AJain9199/AOS16/AOS16 Register/AOS16 Register.kicad_pcb

## KiCad design AOS16 Register/AOS16 Register.kicad_pcb (2025-02-15)

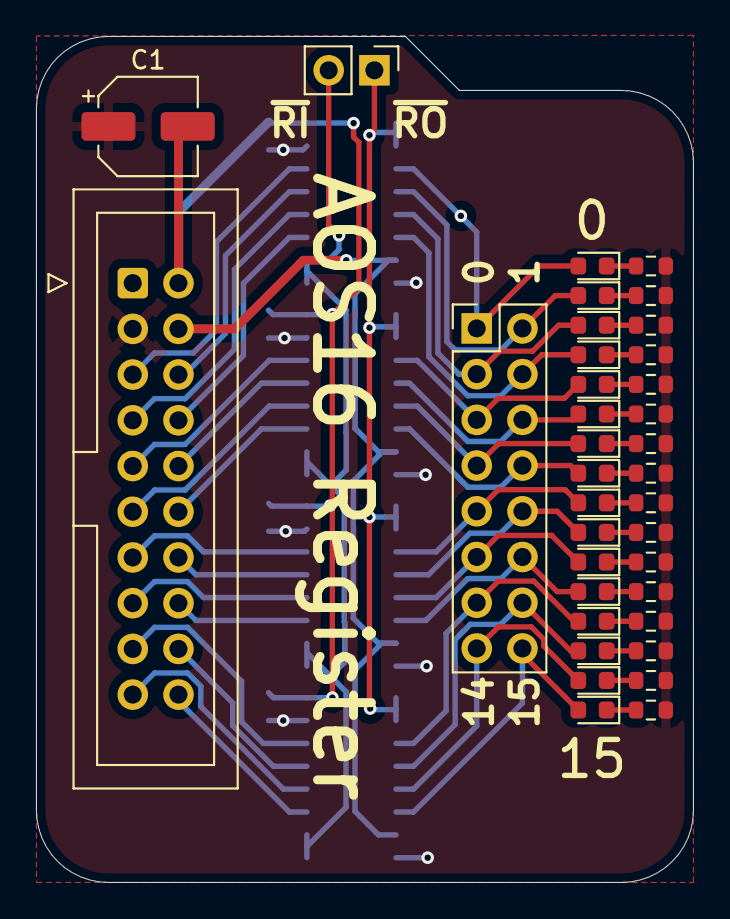
[picture p50: board AOS16 Register.kicad_pcb from above]

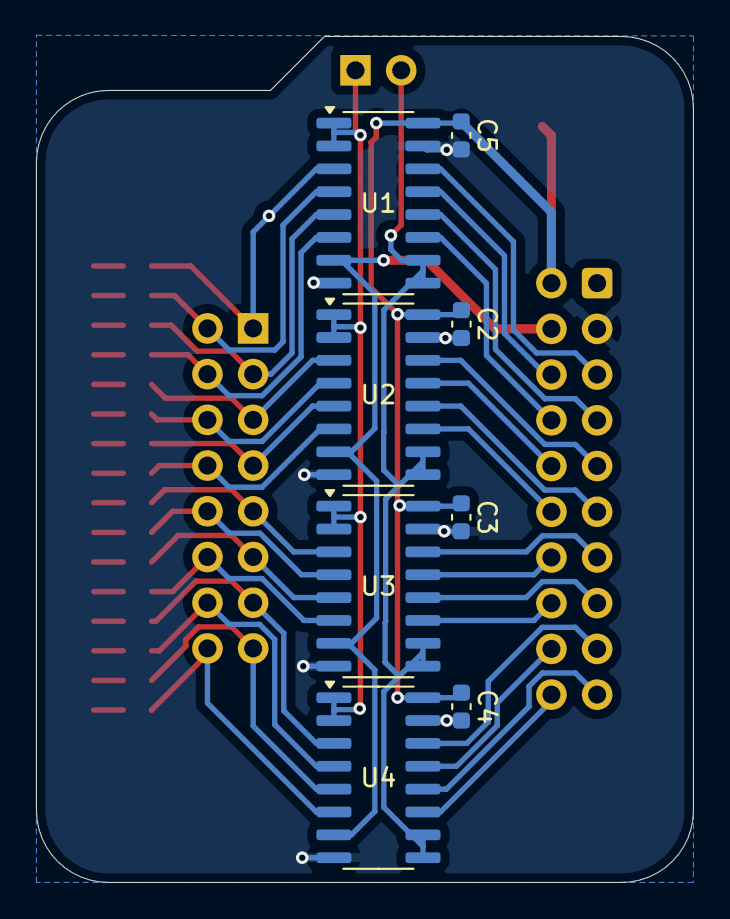
[picture p51: board AOS16 Register.kicad_pcb from below]

Board: 2 copper layers, 36.5 x 47.0 mm, 44 parts (8 on the bottom side), 53 nets.

Parts:
C1: 100uF; CP_Elec_5x5.3
C2, C3, C4, C5: 0.1uF; C_0603_1608Metric
D1, D2, D3, D4, D5, D6, D7, D8, D9, D10, D11, D12, D13, D14, D15, D16: LED; LED_0603_1608Metric
J1: Conn_01x02_Pin; PinHeader_1x02_P2.54mm_Vertical
J2: Conn_02x10_Odd_Even; IDC-Header_2x10_P2.54mm_Vertical
J3: Conn_02x08_Top_Bottom; PinHeader_2x08_P2.54mm_Vertical
R1, R2, R3, R4, R5, R6, R7, R8, R9, R10, R11, R12, R13, R14, R15, R16: R_Small; R_0603_1608Metric
U1, U2, U3, U4: 74HC173; SOIC-16_3.9x9.9mm_P1.27mm

Connections:
/CLK: J2.4, U1.7 (Cp), U2.7 (Cp), U3.7 (Cp), U4.7 (Cp)
/DOUT0: D1.2 (A), J3.1, U1.3 (Q0)
/DOUT1: D2.2 (A), J3.2, U1.4 (Q1)
/DOUT2: D3.2 (A), J3.3, U1.5 (Q2)
/DOUT3: D4.2 (A), J3.4, U1.6 (Q3)
/DOUT4: D5.2 (A), J3.5, U2.3 (Q0)
/DOUT5: D6.2 (A), J3.6, U2.4 (Q1)
/DOUT6: D7.2 (A), J3.7, U2.5 (Q2)
/DOUT7: D8.2 (A), J3.8, U2.6 (Q3)
/DOUT8: D9.2 (A), J3.9, U3.3 (Q0)
/DOUT9: D10.2 (A), J3.10, U3.4 (Q1)
/DOUT10: D11.2 (A), J3.11, U3.5 (Q2)
/DOUT11: D12.2 (A), J3.12, U3.6 (Q3)
/DOUT12: D13.2 (A), J3.13, U4.3 (Q0)
/DOUT13: D14.2 (A), J3.14, U4.4 (Q1)
/DOUT14: D15.2 (A), J3.15, U4.5 (Q2)
/DOUT15: D16.2 (A), J3.16, U4.6 (Q3)
/IO0: J2.5, U1.14 (D0)
/IO1: J2.6, U1.13 (D1)
/IO2: J2.7, U1.12 (D2)
/IO3: J2.8, U1.11 (D3)
/IO4: J2.9, U2.14 (D0)
/IO5: J2.10, U2.13 (D1)
/IO6: J2.11, U2.12 (D2)
/IO7: J2.12, U2.11 (D3)
/IO8: J2.13, U3.14 (D0)
/IO9: J2.14, U3.13 (D1)
/IO10: J2.15, U3.12 (D2)
/IO11: J2.16, U3.11 (D3)
/IO12: J2.17, U4.14 (D0)
/IO13: J2.18, U4.13 (D1)
/IO14: J2.19, U4.12 (D2)
/IO15: J2.20, U4.11 (D3)
/~IE: J1.2, U1.9 (E1), U1.10 (E2), U2.9 (E1), U2.10 (E2), U3.9 (E1), U3.10 (E2), U4.9 (E1), U4.10 (E2)
/~OE: J1.1, U1.1 (Oe1), U1.2 (Oe2), U2.1 (Oe1), U2.2 (Oe2), U3.1 (Oe1), U3.2 (Oe2), U4.1 (Oe1), U4.2 (Oe2)
GND: C1.1, C2.2, C3.2, C4.2, C5.2, J2.3, R1.2, R2.2, R3.2, R4.2, R5.2, R6.2, R7.2, R8.2, R9.2, R10.2, R11.2, R12.2, R13.2, R14.2, R15.2, R16.2, U1.8 (GND), U1.15 (Mr), U2.8 (GND), U2.15 (Mr), U3.8 (GND), U3.15 (Mr), U4.8 (GND), U4.15 (Mr)
unnamed: D1.1 (K), R1.1
unnamed: D2.1 (K), R2.1
unnamed: D3.1 (K), R3.1
unnamed: D4.1 (K), R4.1
unnamed: D5.1 (K), R5.1
unnamed: D6.1 (K), R6.1
unnamed: D7.1 (K), R7.1
unnamed: D8.1 (K), R8.1
unnamed: D9.1 (K), R9.1
unnamed: D10.1 (K), R10.1
unnamed: D11.1 (K), R11.1
unnamed: D12.1 (K), R12.1
unnamed: D13.1 (K), R13.1
unnamed: D14.1 (K), R14.1
unnamed: D15.1 (K), R15.1
unnamed: D16.1 (K), R16.1
VCC: C1.2, C2.1, C3.1, C4.1, C5.1, J2.2, U1.16 (VCC), U2.16 (VCC), U3.16 (VCC), U4.16 (VCC)
