AJain9199/AOS16/assembler/include/parse.h

#ifndef PARSE_H
#define PARSE_H

#include <instruction.h>
#include <operand.h>
#include <map>
#include <memory>
#include <lexer.h>
#include <preprocessor.h>
#include <string>

static std::map<std::string, int> regtab;
static std::map<std::string, std::shared_ptr<Instruction>> opcodes;
void add_opcode(const std::string &name, uint8_t opcode, const std::initializer_list<unsigned char> &operands);
void add_register(const std::string& name, int val);

enum class Section { NONE, DATA, TEXT };

/*
 * Container class for parsing the assembly code
 */
class Parser {
public:
    explicit Parser(const std::string &filename) : lexer(filename, preprocess(filename)) {
    }

    void parse();
    void write_machine_code(const std::string &filename) const;

private:
    struct MachineCodeInstance {
        bool is_constant = false;
        uint16_t constant = 0;

        std::shared_ptr<Instruction> instruction;
        std::vector<std::shared_ptr<Operand>> operands;

        explicit MachineCodeInstance(const uint16_t constant) : is_constant(true), constant(constant) {
        }

        MachineCodeInstance(const std::shared_ptr<Instruction> &instr, const std::vector<std::shared_ptr<Operand>> &operands) : instruction(instr), operands(operands) {}
    };

    std::vector<MachineCodeInstance> machine_code;
    std::vector<MachineCodeInstance> data_code;
    std::vector<MachineCodeInstance> text_code;

    void add_machine_code(const std::shared_ptr<Instruction>& instr, const std::vector<std::shared_ptr<Operand>>& operands);
    void add_machine_code(uint16_t constant);

    static uint16_t section_word_count(const std::vector<MachineCodeInstance>& code);
    static void emit_section(std::fstream& out, const std::vector<MachineCodeInstance>& code);

    Section current_section = Section::NONE;
    bool has_sections = false;

    std::map<std::string, int> symtab;
    void define_label(const std::string &name, int val);

    // labels not yet defined in the symbol table are registered for "future resolution"
    // define_label() will resolve these labels
    std::map<std::string, std::vector<std::shared_ptr<Operand>>> future_resolution;

    uint16_t current_address = 0;

    // parser methods
    void parseStatement();
    void parseDirective();
    void parseDd();
    std::vector<std::shared_ptr<Operand>> parseOperands();
    std::shared_ptr<Operand> parseOperand();
    std::shared_ptr<Operand> parseSubOperand();

    void err(const std::string &msg) {
        error(lexer.getLocation(), msg);
    }

    Lexer lexer;
};

#endif //PARSE_H
